Phedro-Shousa/EIT_RPi_Shield/Code/Mux/ADG725.py

import spidev
import RPi.GPIO as GPIO

# Constants for ADG725 commands
ADG725_ALLOFF = 0x80
ADG725_A_ONLY = 0x20
ADG725_B_ONLY = 0x40

class ADG725:
    def __init__(self, mux1=True):
        GPIO.setmode(GPIO.BCM)
        # Set the SPI bus and select the correct chip select (CS) based on the flag
        if mux1:
            # If mux1, use chip select CS 3
            self.spi = spidev.SpiDev(6, 3)
        else:
            # Otherwise, use chip select CS 1 for mux2
            self.spi = spidev.SpiDev(6, 0)
        # Configure SPI parameters
        self.spi.max_speed_hz = 1000000
        self.spi.mode = 0b01

    def setChannel(self, channel):
        self.spi.xfer([channel & 0x0F])

    def setChannelA(self, channel):
        self.spi.xfer([ADG725_A_ONLY | (channel & 0x0F)])

    def setChannelB(self, channel):
        self.spi.xfer([ADG725_B_ONLY | (channel & 0x0F)])

    def allOff(self):
        self.spi.xfer([ADG725_ALLOFF])

    def setAll(self):
        for i in range(16):
            self.spi.xfer([i & 0x0F])

    def setAllA(self):
        for i in range(16):
            self.spi.xfer([ADG725_A_ONLY | (i & 0x0F)])

    def setAllB(self):
        for i in range(16):
            self.spi.xfer([ADG725_B_ONLY | (i & 0x0F)])

    def channelCount(self):
        return 16
